ploopyco/classic-trackball/hardware/Mechanicals/STLs/Revision C/Bottom.STL

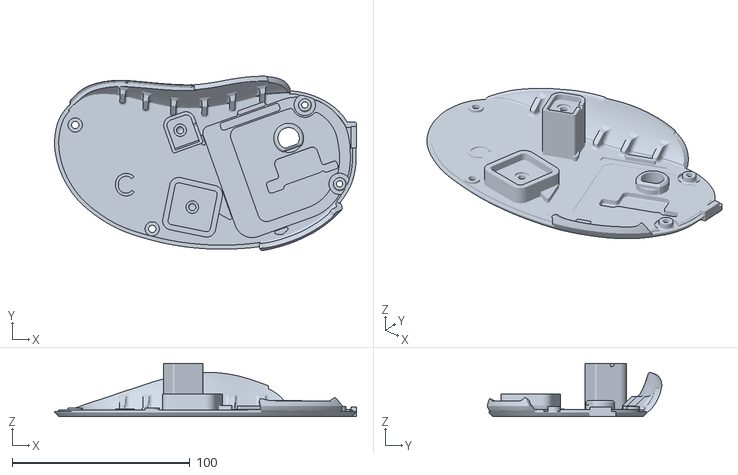
[picture p18: CAD file, 2021-12-14, an earlier design]
hardware/Mechanicals/STLs/Revision C/Bottom.STL
170.0 x 98.3 x 30.0
