ploopyco/classic-trackball/firmware/production/AdvMouse.cpp

/*
  AdvMouse.cpp

  Copyright (c) 2015, Arduino LLC
  Original code (pre-library): Copyright (c) 2011, Peter Barrett

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
  You should have received a copy of the GNU Lesser General Public
  License along with this library; if not, write to the Free Software
  Foundation, Inc., 51 Franklin St, Fifth Floor, Boston, MA  02110-1301  USA
*/

#include "AdvMouse.h"

#if defined(_USING_HID)

// Report format borrowed from bst's bst3360_public.zip
// https://www.overclock.net/forum/375-mice/1561041-reverse-engineering-3366-a-35.html#post26314321
static const uint8_t _hidReportDescriptor[] PROGMEM = {
  0x05, 0x01,   // Usage Page (Generic Desktop)
  0x09, 0x02,   // Usage (Mouse)
  0xA1, 0x01,   // Collection (Application)
    0x85, 0x01,   // HID report ID = 1 
    0x05, 0x09,   //   Usage Page (Button)
      0x19, 0x01,   //   Usage Minimum (Button #1)
      0x29, 0x05,   //   Usage Maximum (Button #5)
      0x15, 0x00,   //   Logical Minimum (0)
      0x25, 0x01,   //   Logical Maximum (1)
      0x95, 0x05,   //   Report Count (5)
      0x75, 0x01,   //   Report Size (1)
      0x81, 0x02,   //   Input (Data, Variable, Absolute)
      0x95, 0x01,   //   Report Count (1)
      0x75, 0x03,   //   Report Size (3)
      0x81, 0x03,   //   Input (Constant) // Byte 1
    0x05, 0x01,   //   Usage Page (Generic Desktop)
      0x09, 0x30,   //   Usage (X)
      0x09, 0x31,   //   Usage (Y)
      0x16, 0x00, 0x80, //   Logical Minimum (-32,768)
      0x26, 0xFF, 0x7F, //   Logical Maximum (32,767)
      0x36, 0x00, 0x80, //   Physical Minimum (-32,768)
      0x46, 0xFF, 0x7F, //   Physical Maxiumum (32,767)
      0x75, 0x10,   //   Report Size (16),
      0x95, 0x02,   //   Report Count (2),
      0x81, 0x06,   //   Input (Data, Variable, Relative) // Byte 3, 5
      0x09, 0x38,   //   Usage (Wheel)
      0x15, 0x81,   //   Logical Minimum (-127)
      0x25, 0x7F,   //   Logical Maximum (127)
      0x35, 0x81,   //   Phyiscal Minimum (-127)
      0x45, 0x7F,   //   Physical Maxiumum (127)
      0x75, 0x08,   //   Report Size (8)
      0x95, 0x01,   //   Report Count (1)
      0x81, 0x06,   //   Input (Data, Variable, Relative) // Byte 6
  0xC0      // End Collection
};


//================================================================================
//================================================================================
//	Mouse

AdvMouse_::AdvMouse_(void) : _buttons(0)
{
    static HIDSubDescriptor node(_hidReportDescriptor, sizeof(_hidReportDescriptor));
    HID().AppendDescriptor(&node);
}

void AdvMouse_::begin(void) 
{
  _isReportSent = false;
}

void AdvMouse_::end(void) 
{
}

void AdvMouse_::click(uint8_t b)
{
	_buttons = b;
	move(0,0,0);
	_buttons = 0;
	move(0,0,0);
}

bool AdvMouse_::needSendReport(void)
{
  return !_isReportSent;
}

void AdvMouse_::move(int16_t x, int16_t y, signed char wheel)
{
	uint8_t m[6];
	m[0] = _buttons;
  m[1] = x & 0xFF;
  m[2] = (x>>8) & 0xFF;
  m[3] = y & 0xFF;
  m[4] = (y>>8) & 0xFF;
  m[5] = wheel;
	HID().SendReport(1,m,6);
  _isReportSent = true;
}

void AdvMouse_::buttonsWithoutMove(uint8_t b)
{
  if (b != _buttons)
  {
    _buttons = b;
    _isReportSent = false;
  }
}

void AdvMouse_::buttons(uint8_t b)
{
	if (b != _buttons)
	{
		_buttons = b;
		move(0,0,0);   
	}
}

void AdvMouse_::press(uint8_t b) 
{
	buttons(_buttons | b);
}

void AdvMouse_::release(uint8_t b)
{
	buttons(_buttons & ~b);
}

void AdvMouse_::press_(uint8_t b) 
{
  buttonsWithoutMove(_buttons | b);
}

void AdvMouse_::release_(uint8_t b)
{
  buttonsWithoutMove(_buttons & ~b);
}


bool AdvMouse_::isPressed(uint8_t b)
{
	if ((b & _buttons) > 0) 
		return true;
	return false;
}

AdvMouse_ AdvMouse;

#endif
